josefprusa/Prusa3/box_frame/doc/framestep1.png

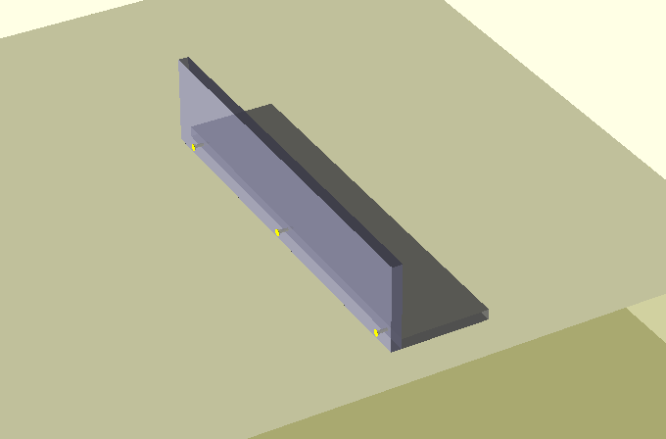
box_frame/doc/framestep1.png
