josefprusa/Prusa3/box_frame/doc/framestep2.png

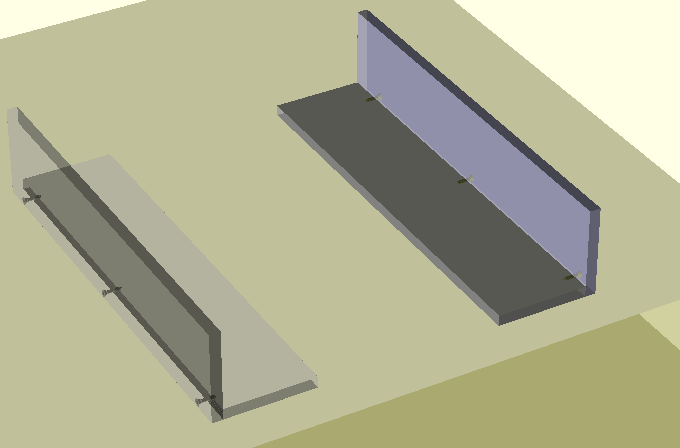
box_frame/doc/framestep2.png
