josefprusa/Prusa3/box_frame/doc/framestep4.png

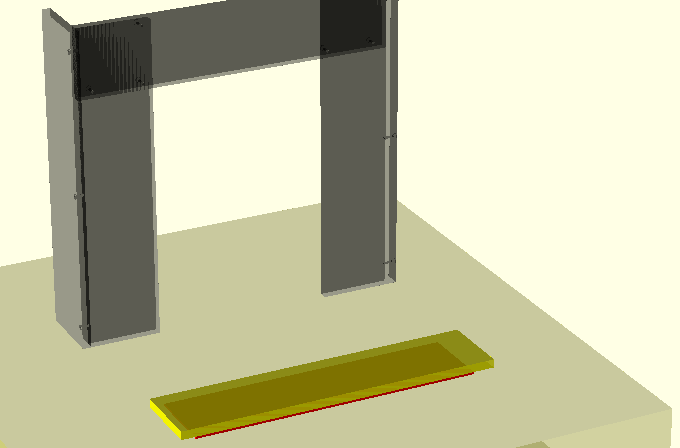
box_frame/doc/framestep4.png
