josefprusa/Prusa3/box_frame/doc/framestep5.png

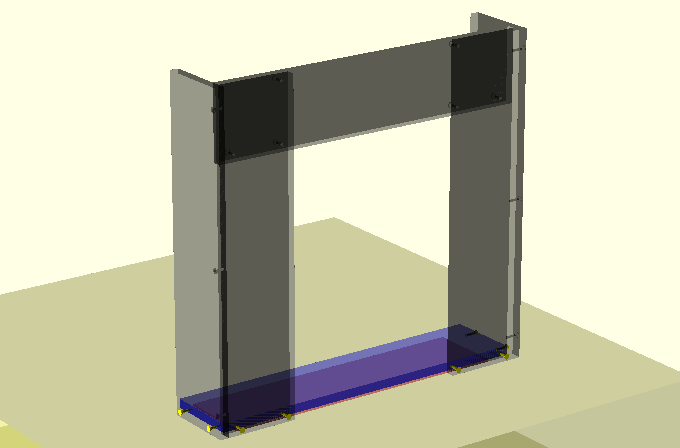
box_frame/doc/framestep5.png
