josefprusa/Prusa3/box_frame/doc/ystep2.png

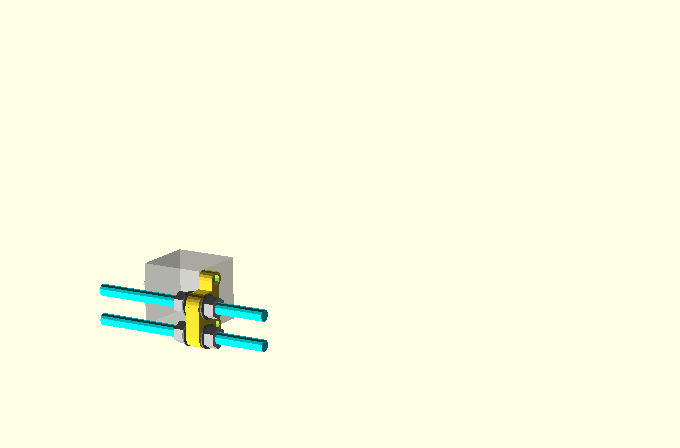
box_frame/doc/ystep2.png
