josefprusa/Prusa3/box_frame/doc/ystep4.png

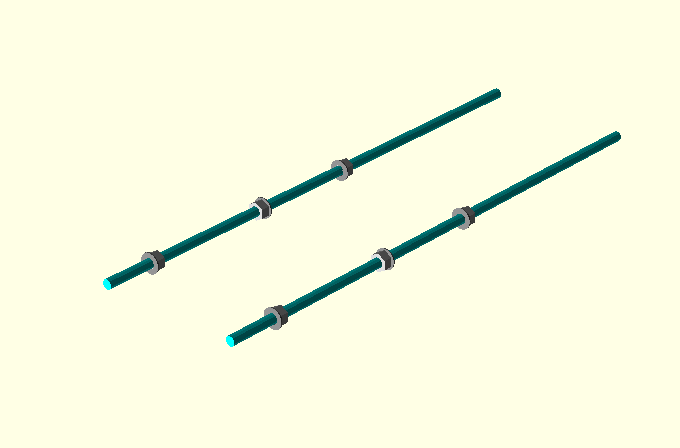
box_frame/doc/ystep4.png
