josefprusa/Prusa3/box_frame/doc/ystep6.png

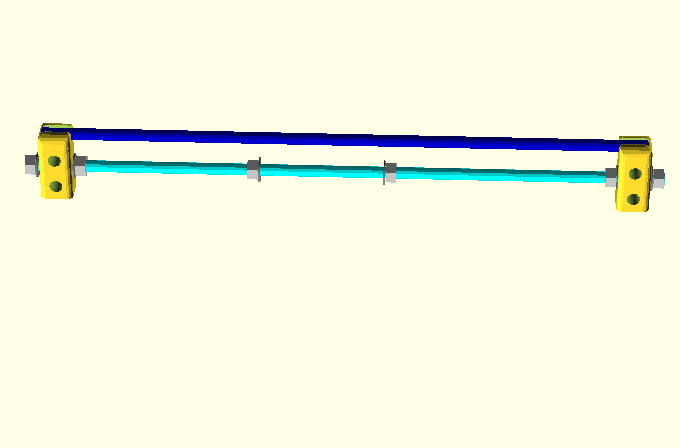
box_frame/doc/ystep6.png
