josefprusa/Prusa3/box_frame/doc/ystep8.png

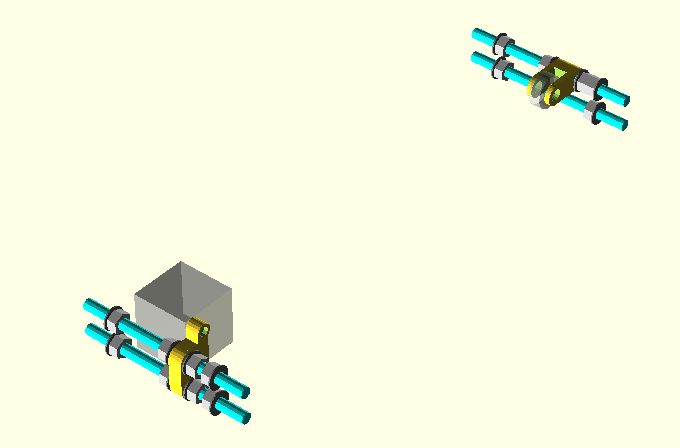
box_frame/doc/ystep8.png
