josefprusa/Prusa3/box_frame/doc/ystep9.png

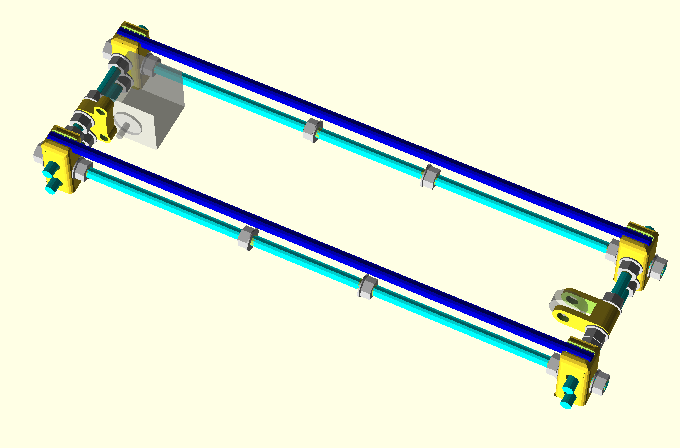
box_frame/doc/ystep9.png
