josefprusa/Prusa3/box_frame/doc/ystep10.png

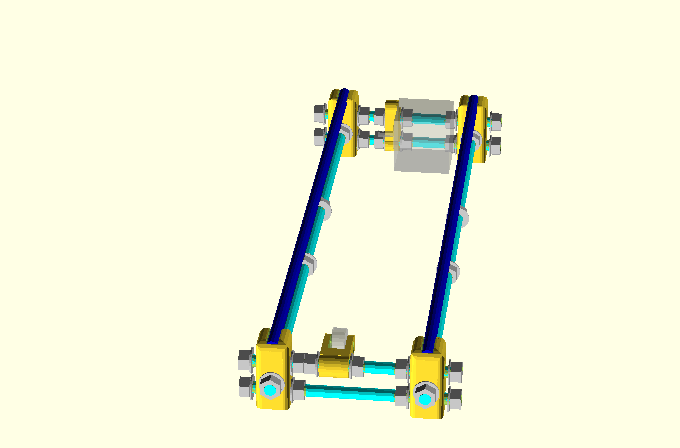
box_frame/doc/ystep10.png
