josefprusa/Prusa3/box_frame/doc/ystep11.png

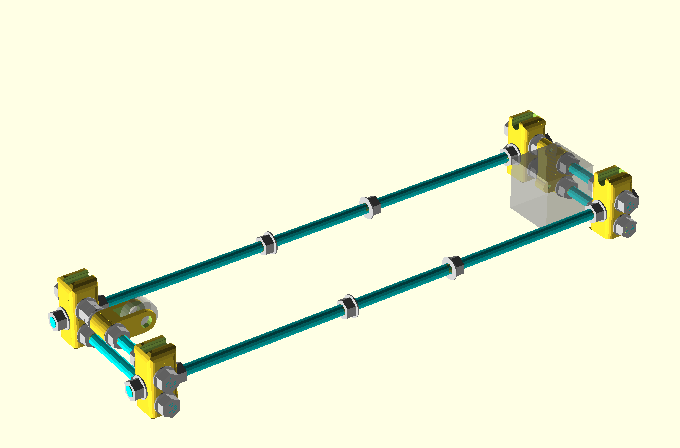
box_frame/doc/ystep11.png
