josefprusa/Prusa3/box_frame/sample_stls/big_htd3_lm12luu/y-drivetrain.stl

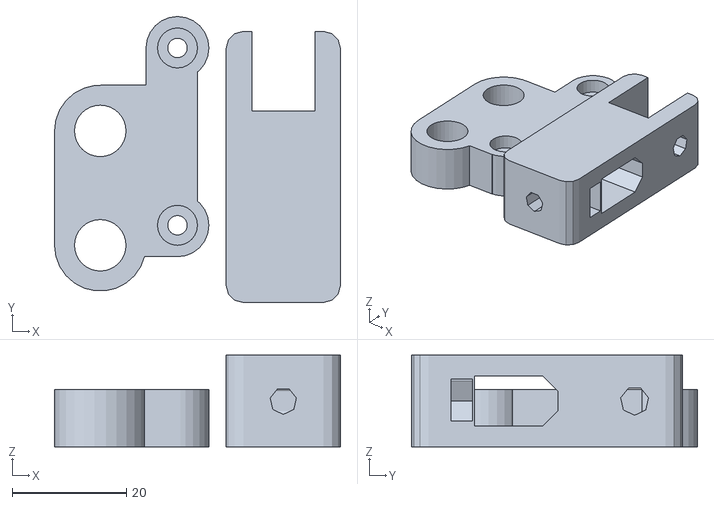
[picture p31: CAD file, 2013-10-11]
box_frame/sample_stls/big_htd3_lm12luu/y-drivetrain.stl
50.0 x 50.0 x 16.0
