josefprusa/Prusa3/box_frame/sample_stls/default_box_gt2_lm10uu/bushing.stl

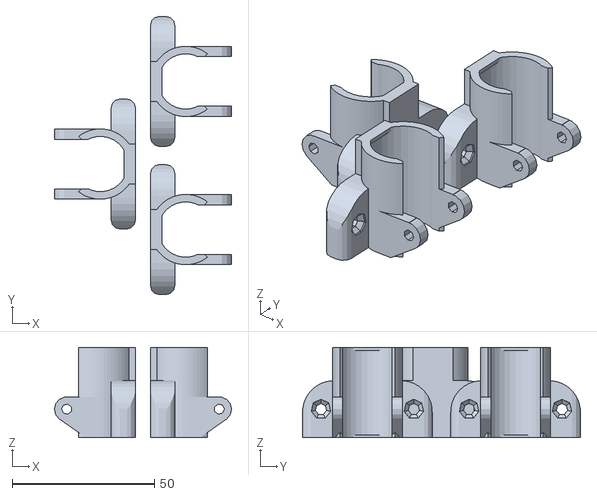
[picture p32: CAD file, 2013-12-24]
box_frame/sample_stls/default_box_gt2_lm10uu/bushing.stl
62.2 x 97.6 x 31.7
