josefprusa/Prusa3/box_frame/sample_stls/default_box_gt2_lm10uu/extras/tube_clamp.stl

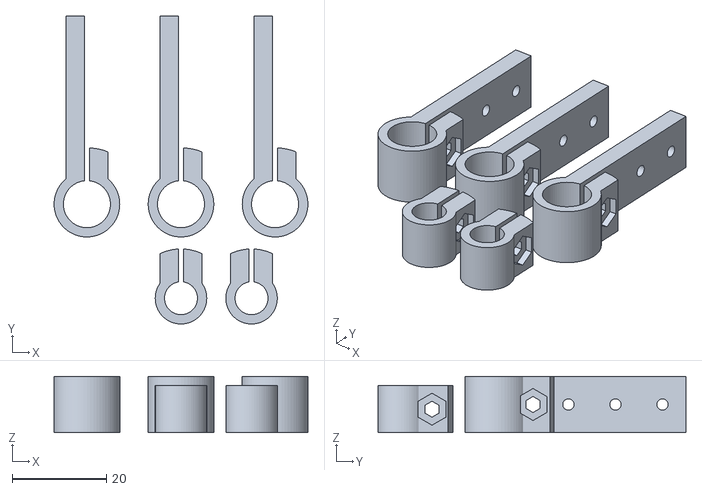
[picture p33: CAD file, 2013-12-24]
box_frame/sample_stls/default_box_gt2_lm10uu/extras/tube_clamp.stl
54.0 x 65.5 x 12.0
