josefprusa/Prusa3/box_frame/sample_stls/single_plate_gt2_lm8uu/y-belt-holder.stl

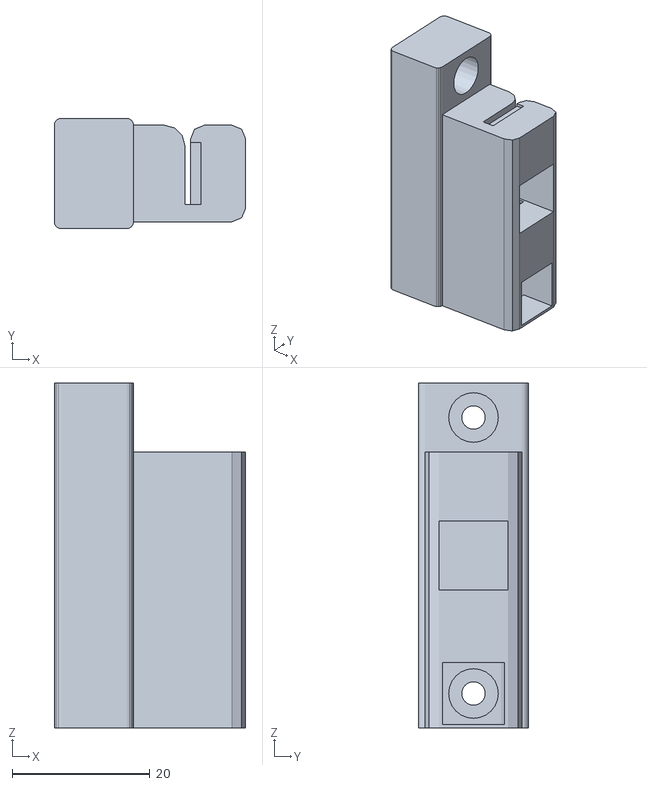
[picture p34: CAD file, 2013-12-24]
box_frame/sample_stls/single_plate_gt2_lm8uu/y-belt-holder.stl
27.8 x 16.0 x 50.0
