josefprusa/Prusa3/mini/extruder/mgs/mgs-idler.stl

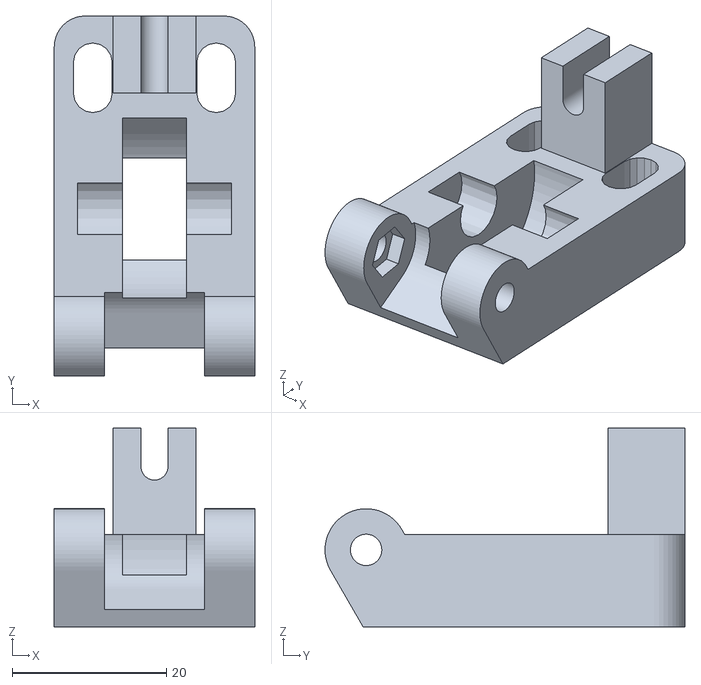
[picture p35: CAD file, 2013-01-09]
mini/extruder/mgs/mgs-idler.stl
26.0 x 46.7 x 25.8
