josefprusa/Prusa3/mini/y-bushing_1x.stl

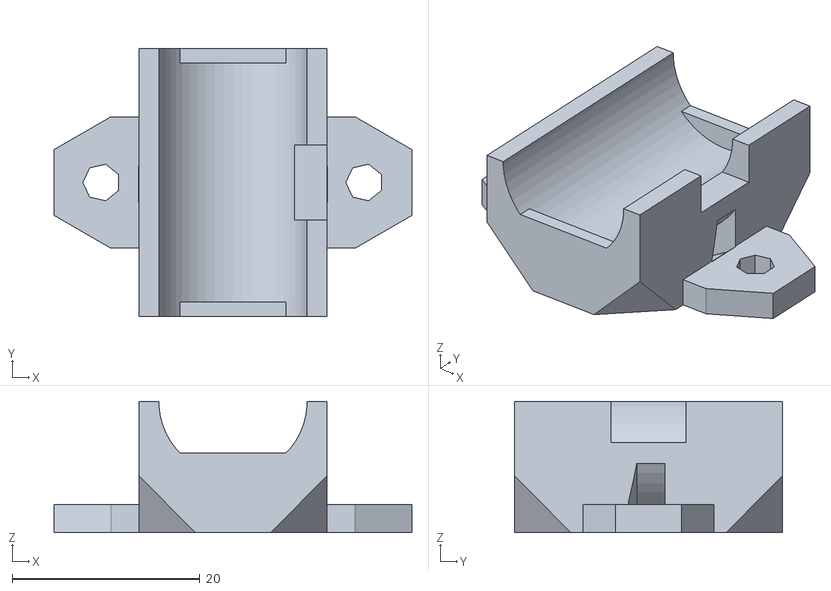
[picture p36: CAD file, 2013-01-09]
mini/y-bushing_1x.stl
38.1 x 28.5 x 14.0
