josefprusa/Prusa3/single_plate/src/frame/6mm/Prusa3ALU-FREZOVANY-v4.dxf

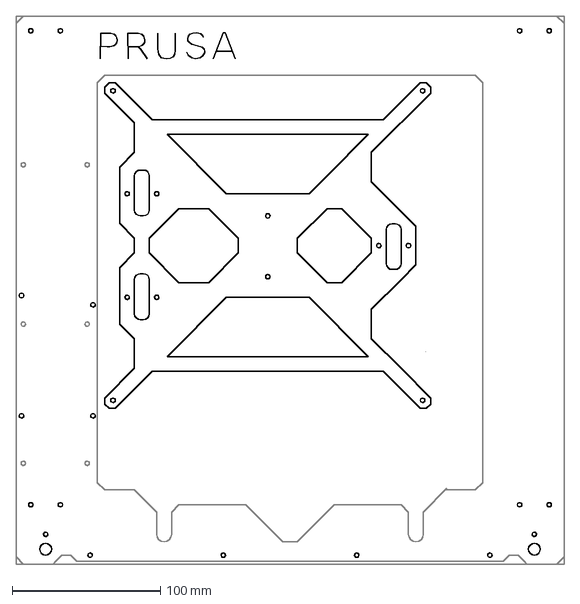
[picture p37: CAD file, 2013-01-09]
single_plate/src/frame/6mm/Prusa3ALU-FREZOVANY-v4.dxf
370.0 x 370.0 mm
