josefprusa/Prusa3/box_frame/sample_stls/big_htd3_lm12luu/z-axis.stl

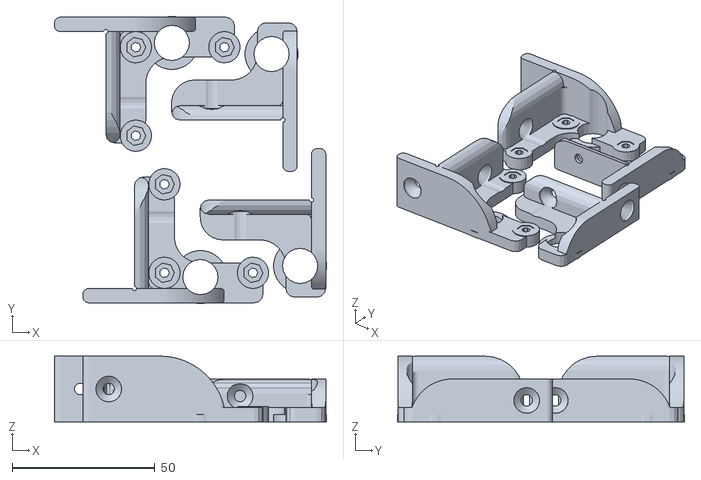
[picture p38: CAD file, 2013-10-11]
box_frame/sample_stls/big_htd3_lm12luu/z-axis.stl
95.2 x 100.5 x 23.0
