josefprusa/Prusa3/box_frame/sample_stls/default_box_gt2_lm10uu/extras/calibrate.stl

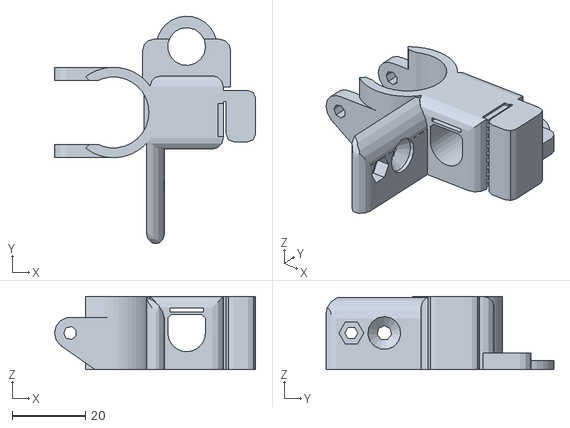
[picture p39: CAD file, 2013-12-24]
box_frame/sample_stls/default_box_gt2_lm10uu/extras/calibrate.stl
54.9 x 62.2 x 20.0
