josefprusa/Prusa3/box_frame/sample_stls/single_plate_gt2_lm8uu/extras/tube_clamp.stl

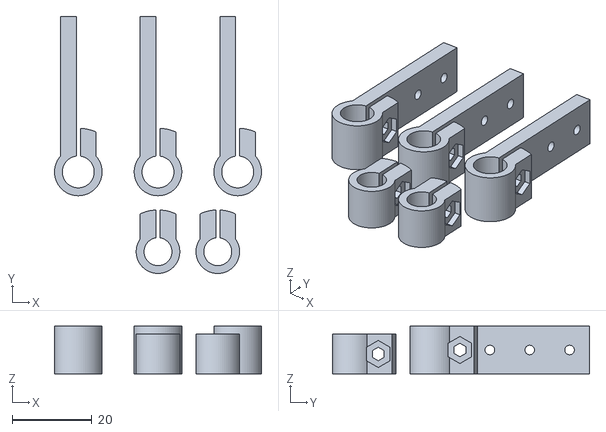
[picture p40: CAD file, 2013-10-11]
box_frame/sample_stls/single_plate_gt2_lm8uu/extras/tube_clamp.stl
52.0 x 64.5 x 12.0
