josefprusa/Prusa3/box_frame/sample_stls/single_plate_gt2_lm8uu/z-axis.stl

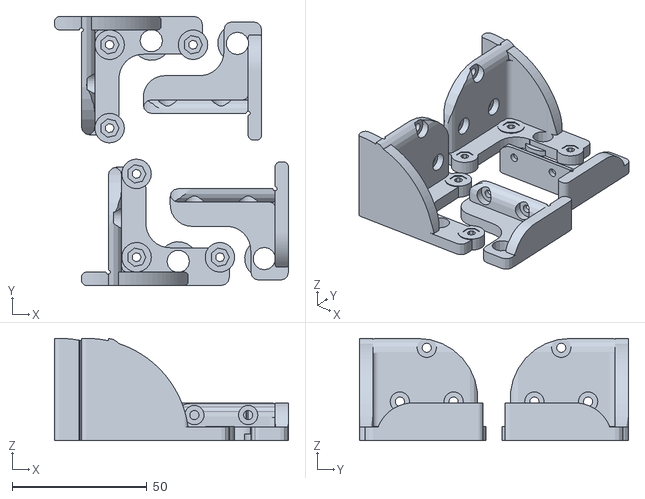
[picture p41: CAD file, 2013-12-24]
box_frame/sample_stls/single_plate_gt2_lm8uu/z-axis.stl
87.0 x 100.0 x 38.0
