josefprusa/Prusa3/mini/extruder/mgs/mgs-groovemount_ABS.stl

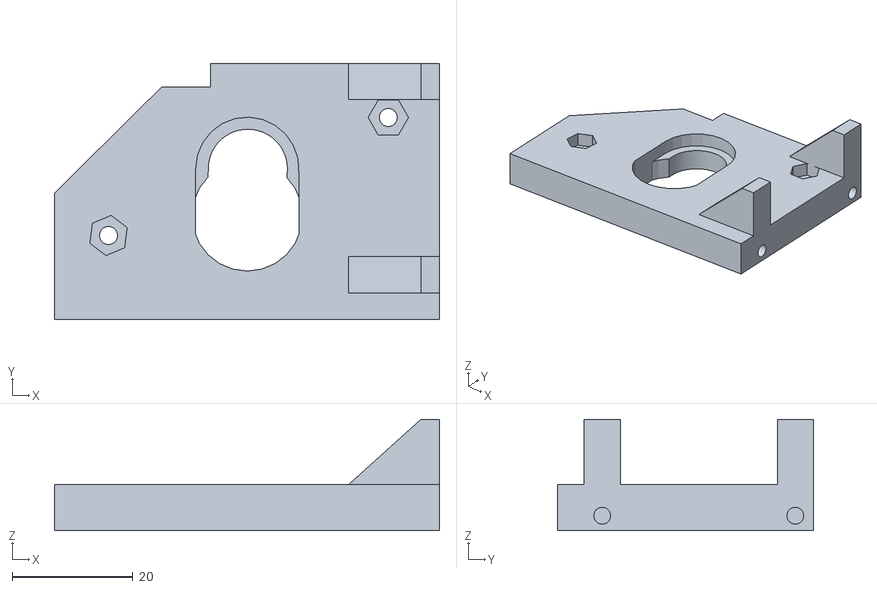
[picture p42: CAD file, 2013-01-09]
mini/extruder/mgs/mgs-groovemount_ABS.stl
63.8 x 42.4 x 18.4
