josefprusa/Prusa3/mini/x-end-motor.stl

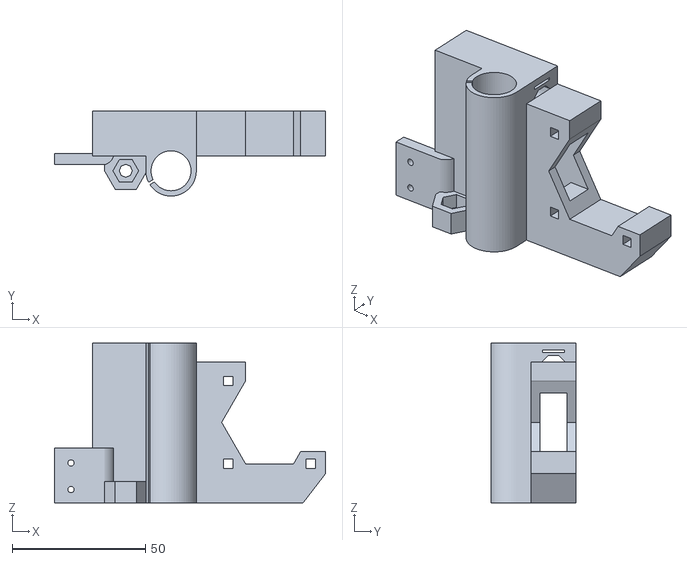
[picture p43: CAD file, 2013-01-09]
mini/x-end-motor.stl
101.8 x 32.0 x 60.0
