josefprusa/Prusa3/single_plate/src/frame/6mm/frame-one-layer.dxf

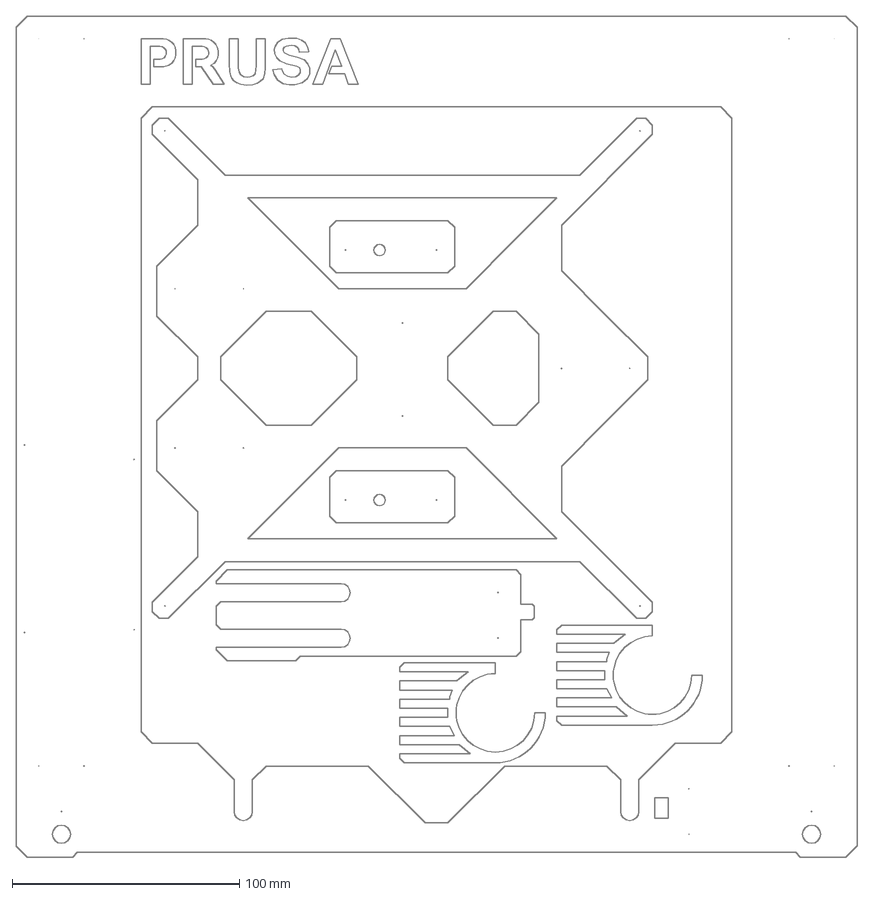
[picture p44: CAD file, 2013-01-09]
single_plate/src/frame/6mm/frame-one-layer.dxf
370.0 x 370.0 mm
