josefprusa/Prusa3/box_frame/sample_stls/big_htd3_lm12luu/y-belt-holder.stl

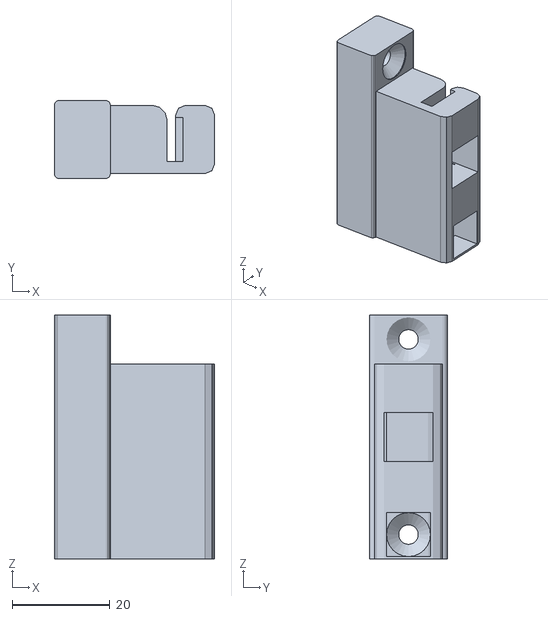
[picture p45: CAD file, 2013-09-17]
box_frame/sample_stls/big_htd3_lm12luu/y-belt-holder.stl
32.9 x 16.0 x 50.0
