josefprusa/Prusa3/box_frame/sample_stls/single_plate_gt2_lm8uu/extras/bearing-holder-single-plate-y.stl

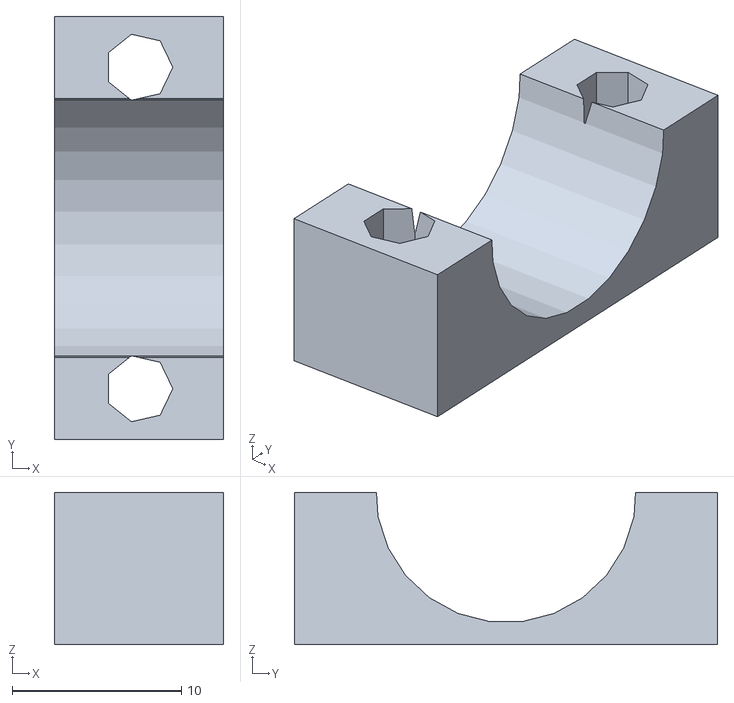
[picture p46: CAD file, 2013-04-29]
box_frame/sample_stls/single_plate_gt2_lm8uu/extras/bearing-holder-single-plate-y.stl
10.0 x 25.0 x 9.00
