josefprusa/Prusa3/box_frame/sample_stls/single_plate_gt2_lm8uu/x-carriage.stl

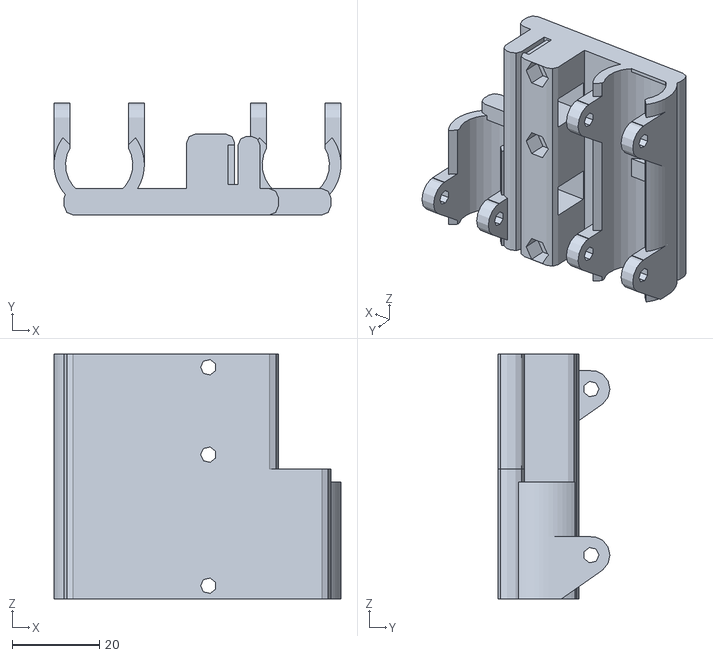
[picture p47: CAD file, 2013-12-24]
box_frame/sample_stls/single_plate_gt2_lm8uu/x-carriage.stl
65.7 x 25.6 x 56.0
