josefprusa/Prusa3/mini/z-bottom-right.stl

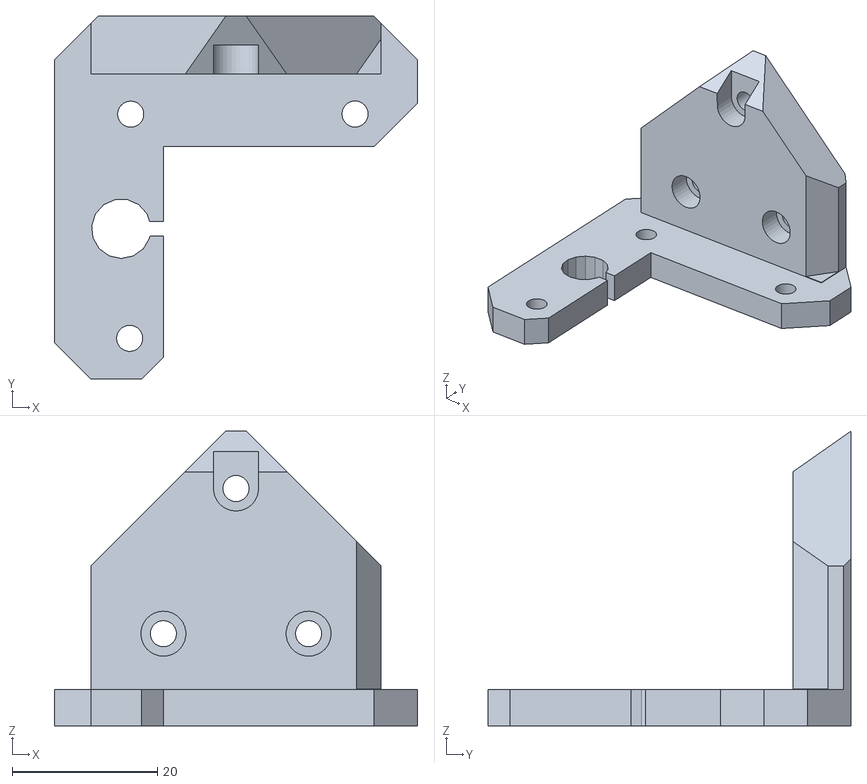
[picture p48: CAD file, 2013-01-09]
mini/z-bottom-right.stl
50.0 x 50.0 x 40.6
