josefprusa/Prusa3/box_frame/sample_stls/big_htd3_lm12luu/x-carriage.stl

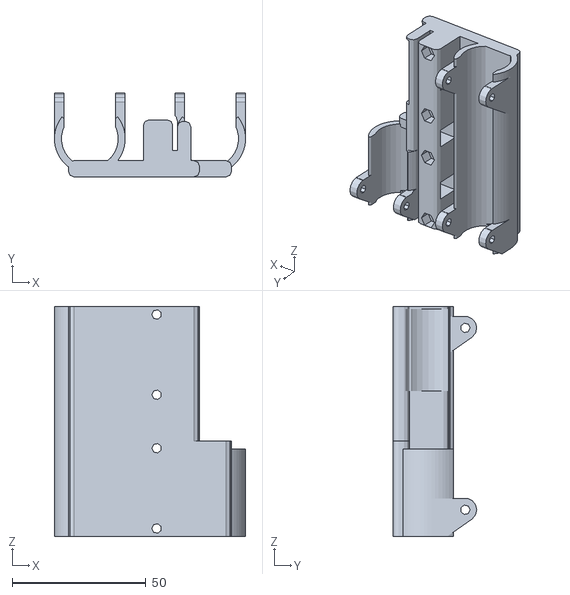
[picture p49: CAD file, 2013-09-17]
box_frame/sample_stls/big_htd3_lm12luu/x-carriage.stl
71.5 x 31.2 x 86.0
