josefprusa/Prusa3/box_frame/sample_stls/default_box_gt2_lm10uu/x-carriage.stl

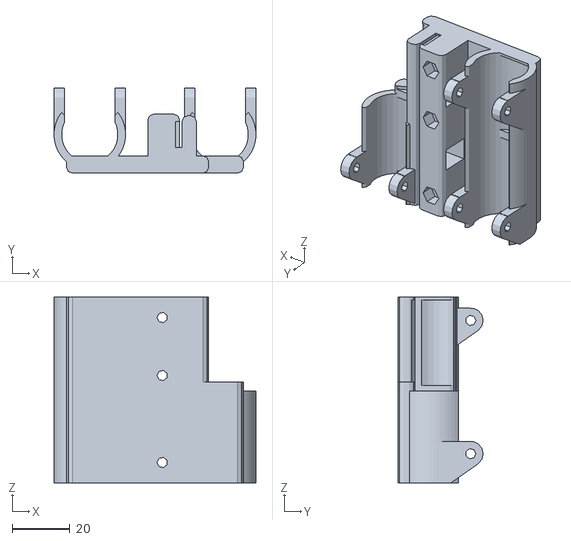
[picture p50: CAD file, 2013-12-24]
box_frame/sample_stls/default_box_gt2_lm10uu/x-carriage.stl
69.7 x 29.4 x 64.0
