josefprusa/Prusa3/box_frame/sample_stls/single_plate_gt2_lm8uu/x-end.stl

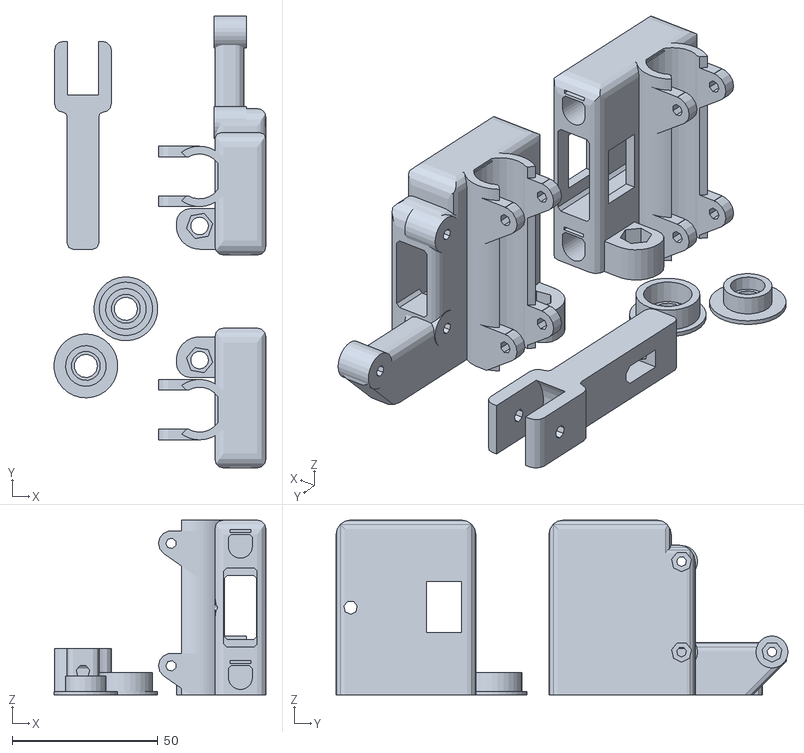
[picture p51: CAD file, 2013-12-24]
box_frame/sample_stls/single_plate_gt2_lm8uu/x-end.stl
72.7 x 155.0 x 60.0
