josefprusa/Prusa3/mini/y-motor.stl

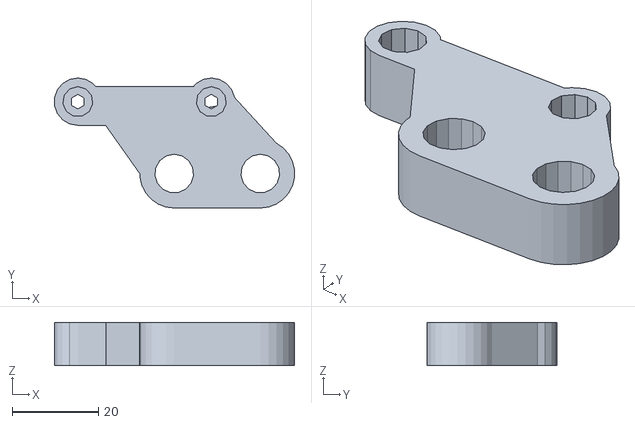
[picture p52: CAD file, 2013-01-09]
mini/y-motor.stl
55.7 x 30.2 x 10.0
