josefprusa/Prusa3/box_frame/sample_stls/default_box_gt2_lm10uu/y-belt-holder.stl

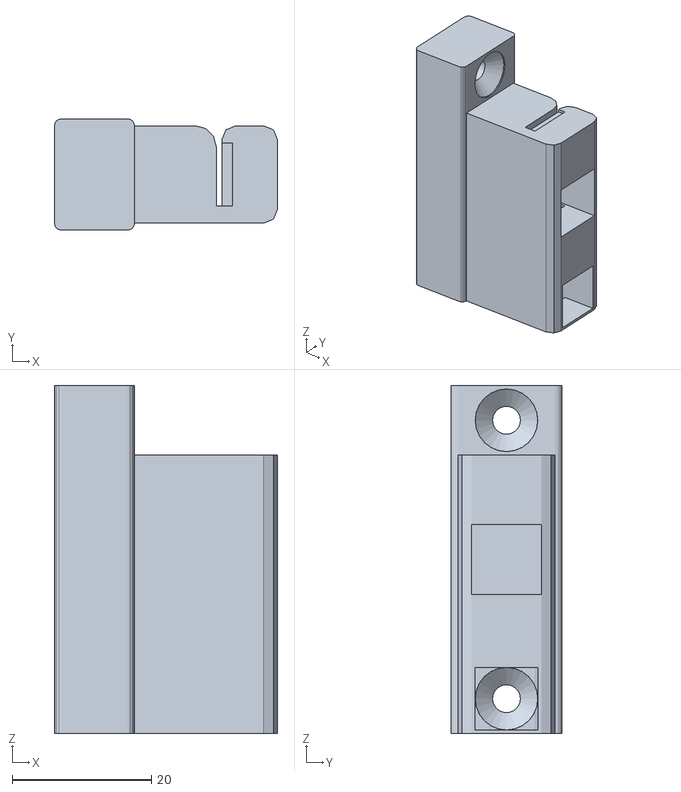
[picture p53: CAD file, 2013-12-24]
box_frame/sample_stls/default_box_gt2_lm10uu/y-belt-holder.stl
32.0 x 16.0 x 50.0
