josefprusa/Prusa3/mini/y-endstop-holder.stl

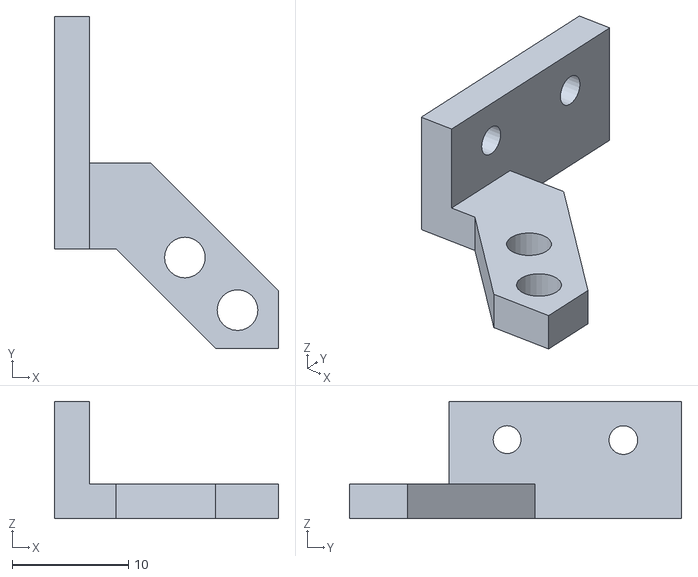
[picture p54: CAD file, 2013-01-09]
mini/y-endstop-holder.stl
19.3 x 28.6 x 10.1
