josefprusa/Prusa3/box_frame/sample_stls/big_htd3_lm12luu/y-axis-bracket.stl

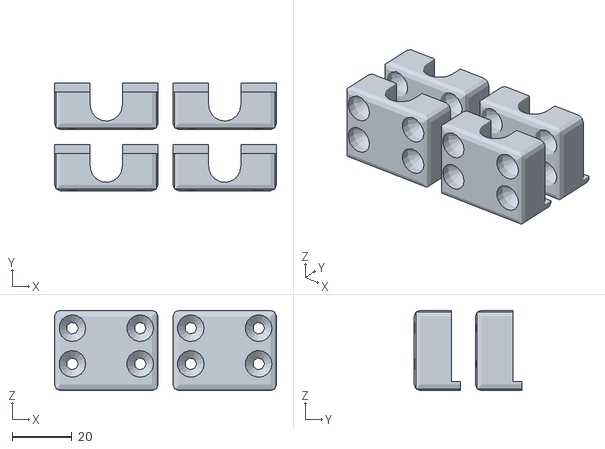
[picture p55: CAD file, 2013-06-04]
box_frame/sample_stls/big_htd3_lm12luu/y-axis-bracket.stl
74.6 x 36.2 x 27.0
