josefprusa/Prusa3/mini/frame-mount.stl

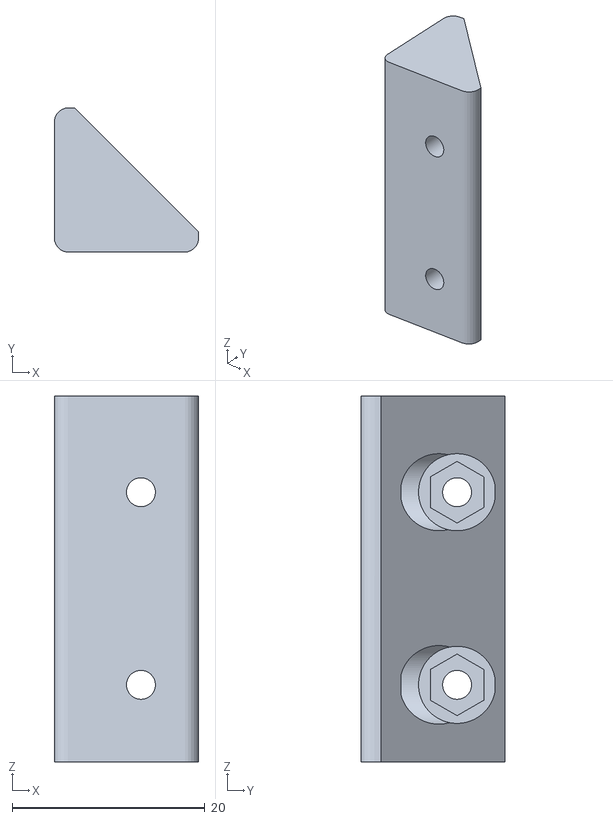
[picture p56: CAD file, 2013-01-09]
mini/frame-mount.stl
15.0 x 15.0 x 38.0
