josefprusa/Prusa3/mini/y-corners_4x.stl

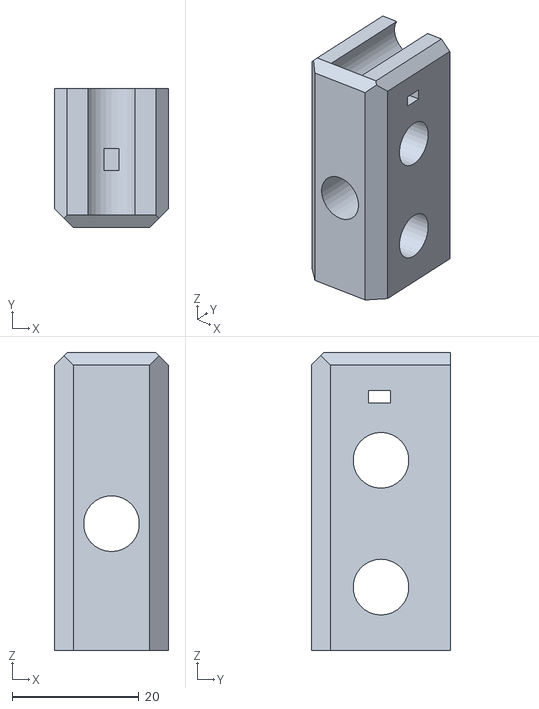
[picture p57: CAD file, 2013-01-09]
mini/y-corners_4x.stl
18.0 x 22.0 x 47.0
