josefprusa/Prusa3/mini/y-belt-holder.stl

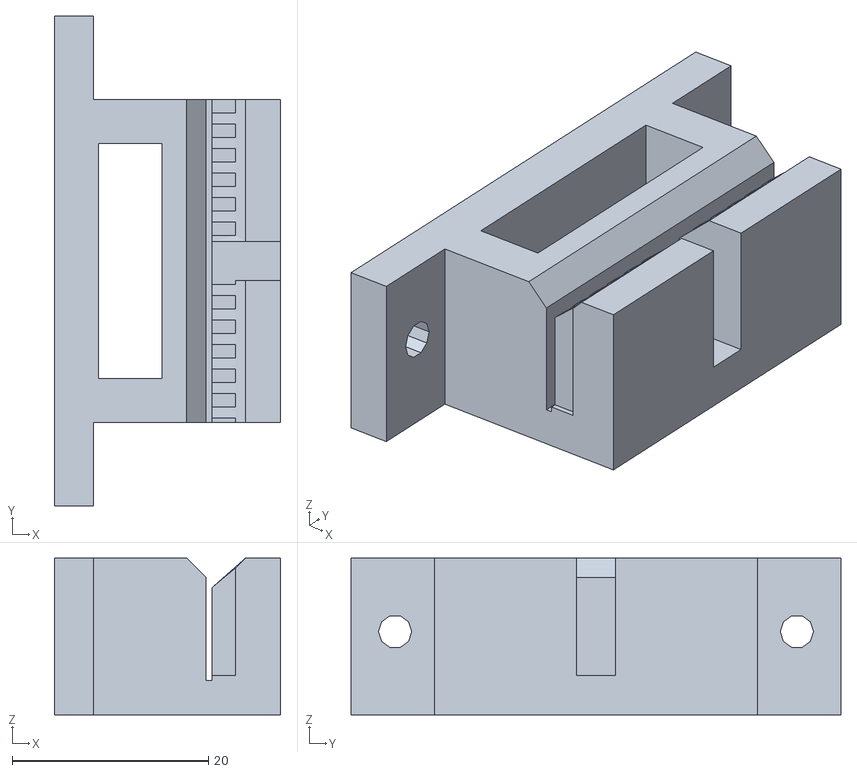
[picture p58: CAD file, 2013-01-09]
mini/y-belt-holder.stl
23.1 x 50.0 x 16.0
