josefprusa/Prusa3/mini/z-top-right.stl

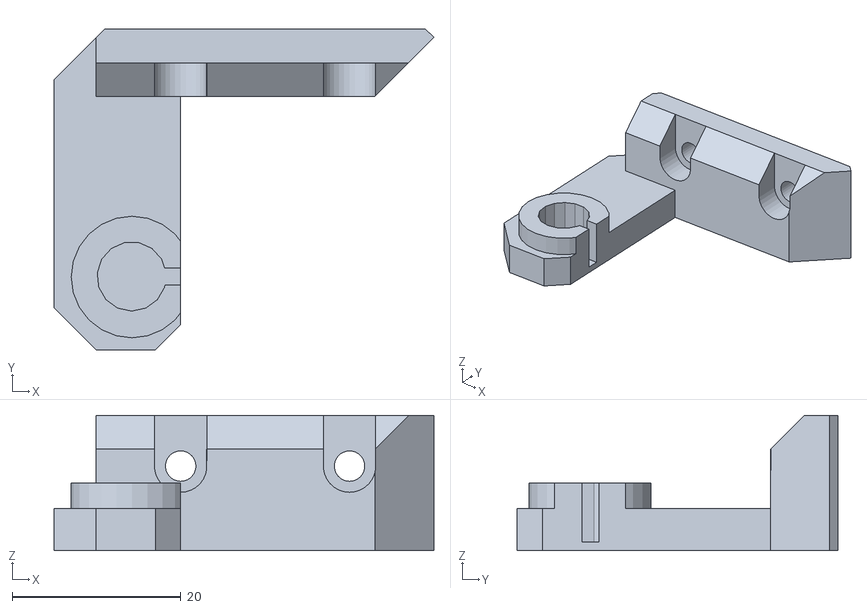
[picture p59: CAD file, 2013-01-09]
mini/z-top-right.stl
45.0 x 38.0 x 16.0
