josefprusa/Prusa3/mini/x-carriage.stl

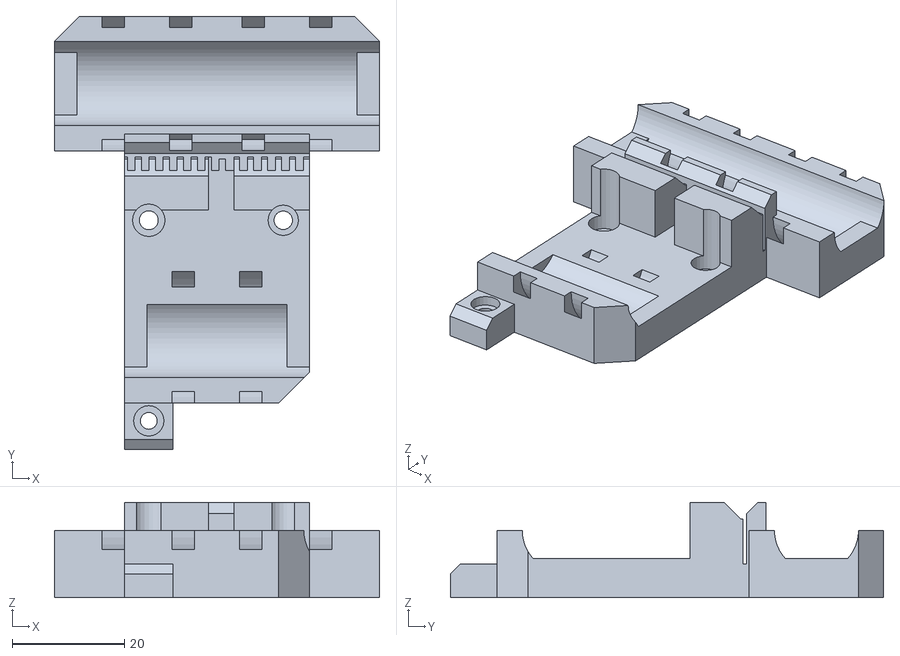
[picture p60: CAD file, 2013-01-09]
mini/x-carriage.stl
58.0 x 77.4 x 17.0
