josefprusa/Prusa3/mini/x-end-idler.stl

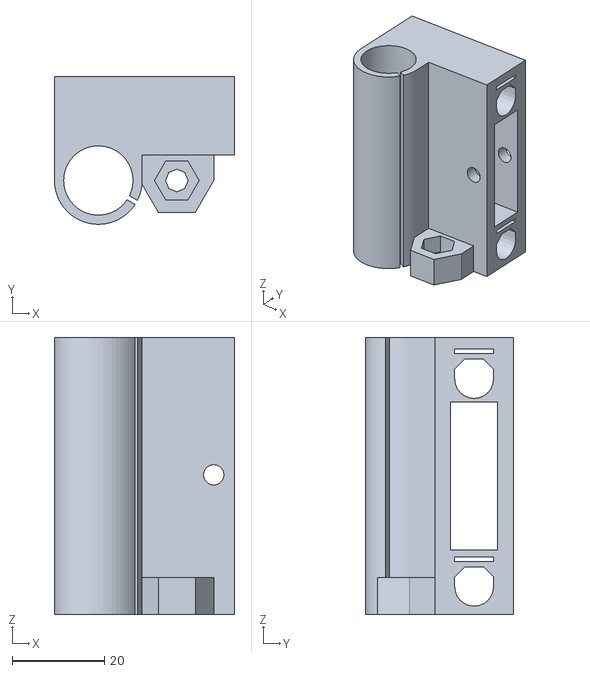
[picture p61: CAD file, 2013-01-09]
mini/x-end-idler.stl
39.0 x 32.0 x 60.0
