josefprusa/Prusa3/mini/z-endstop-holder.stl

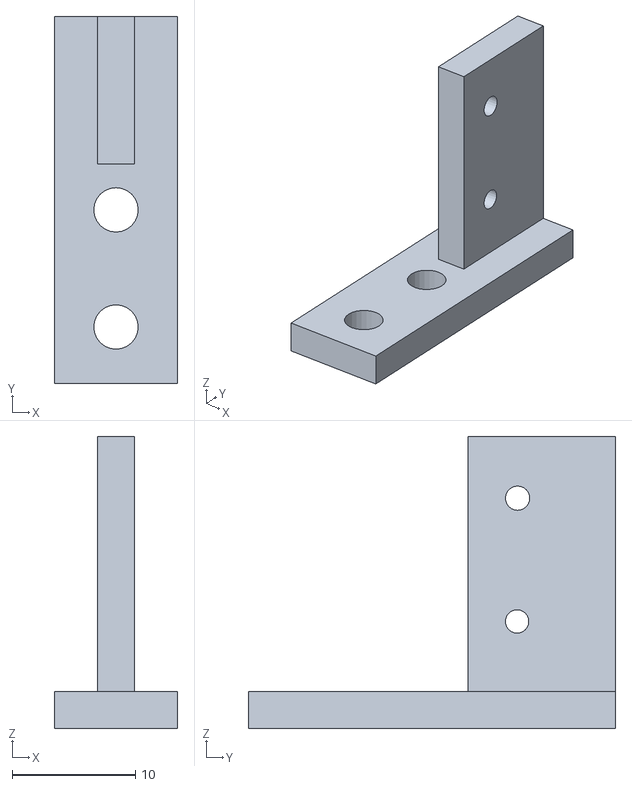
[picture p62: CAD file, 2013-01-09]
mini/z-endstop-holder.stl
10.0 x 29.8 x 23.7
