josefprusa/Prusa3/box_frame/bushing.scad

// PRUSA iteration3
// Bushing/bearing housings
// GNU GPL v3
// Josef Průša <josefprusa@me.com>
// Václav 'ax' Hůla <axtheb@gmail.com>
// http://www.reprap.org/wiki/Prusa_Mendel
// http://github.com/josefprusa/Prusa3

// ThingDoc entry
/**
 * @id yBearingHolder
 * @name Y Axis Bearing Holder
 * @category Printed
 */
 
include <configuration.scad>

// ensure that the part length is at least the length of bushing barrel plus add
function adjust_bushing_len(conf_b, h, add=layer_height*2) = ((conf_b[2]+add) > h) ? conf_b[2]+add : h;

//distance from the flat side of bushing holder to rod center
function bushing_foot_len(conf_b, h=10.5, add=4*single_wall_width) = ((conf_b[1]+add) > h) ? conf_b[1]+add : h;

function bushing_outer_radius(conf_b) = conf_b[1] + 4*single_wall_width;

// basic building blocks, housings for 1 bushing/bearing
// at [0,0] there is center of the smooth rod, pointing in Z

module linear_bushing_negative_single(conf_b=bushing_xy, h=0){
    // barrel with the dimensions of a bushing/bearing
    // to be substracted as needed
    translate([0, 0, -0.01])  cylinder(r = conf_b[1], h = adjust_bushing_len(conf_b, h) + 0.02);
}

module linear_bearing_negative_single(conf_b=bushing_xy, h=0, shadow=false){
    // barrel with the dimensions of the bearing
    translate([0, 0, -0.01 + 3 * layer_height])  cylinder(r = conf_b[1], h = adjust_bushing_len(conf_b, h) + 0.02);
    if (shadow == false) {
        translate([0, -conf_b[1]+1, -0.01 + 3 * layer_height]) cube([30, 2 * conf_b[1] - 2, adjust_bushing_len(conf_b, h) + 0.02]);
    }
}

module linear_bushing_single(conf_b=bushing_xy, h=0) {
    // This is the printed barrel around bushing
    // with foot pointing to -x
    translate([-bushing_foot_len(conf_b), -7, 0]) cube([bushing_foot_len(conf_b), 14, adjust_bushing_len(conf_b, h)]);
    cylinder(r=bushing_outer_radius(conf_b), h=adjust_bushing_len(conf_b, h));
}

module linear_bushing_negative(conf_b=bushing_xy, h=0){
    // return simple negative stretched all along and a smooth rod
    translate([0,0,-0.1]) cylinder(r = conf_b[0] + single_wall_width, h=adjust_bushing_len(conf_b, h)+0.2);
    linear_bushing_negative_single(conf_b, h=adjust_bushing_len(conf_b, h));
}

module linear_bearing_negative(conf_b = bushing_xy, h = 0, shadow=false){
    //same as linear_bushing_negative, but with z direction constrained parts
    translate([0,0,-0.1]) cylinder(r = conf_b[0] + single_wall_width, h=adjust_bushing_len(conf_b, h, 8*layer_height)+0.2);
    //lower bearing
    linear_bearing_negative_single(conf_b, 0, shadow);
    if (h > 2*conf_b[2] + 9*layer_height){
        translate([0,0,h]) mirror([0,0,1]) linear_bearing_negative_single(conf_b, 0, shadow);
    }
}

module linear_negative_preclean(conf_b = bushing_xy) {
    // makes sure there is nothing interfering
    // to be substracted before linear()
    cylinder(r = conf_b[1] + single_wall_width, h=300, center=true);
}

module linear_bushing_sloped(conf_b=bushing_xy, h= 100){
    // cut the bushing at angle, so it can be printed upside down
    intersection(){
        linear_bushing_single(conf_b, h = h);
        // hardcoded, may need fixing for different barelled bushings
        // atm there is only one and I am too lazy
        translate([0, 0, -2]) rotate([0,-50,0]) cube([30, 40, 80], center=true);
    }
}

module linear_bushing(conf_b=bushing_xy, h=0){
    // this is the function to be used for type 1 linears (barrel holder)
    // It has bushing on bottom and for parts longer than 3x the barel length on top too
    difference() {
        union() {
            translate([-bushing_foot_len(conf_b), -7, 0]) cube([2, 14, adjust_bushing_len(conf_b, h)]);
            linear_bushing_single(conf_b);
            if (h>3*conf_b[2]) {
                translate([0,0,h]) mirror([0,0,1]) linear_bushing_sloped(conf_b);
            }
        }
        linear_bushing_negative(conf_b, h);
    }
}

module linear_bearing(conf_b=bushing_xy, h=0){
    difference() {
        union() {
            difference(){
                union(){
                    //main block
                    //translate([-bushing_foot_len(conf_b), -7, 0]) cube([4, 14, adjust_bushing_len(conf_b, h, 9*layer_height)]);   <- removed for duplicity:)
                    translate([0,0,0]) cylinder(h = adjust_bushing_len(conf_b, h, 9*layer_height), r=bushing_outer_radius(conf_b), $fn=60);
                }
                //smooth entry cut
                translate([12,0,-1]) rotate([0,0,45]) cube([20, 20, 200], center=true);
            }
            intersection(){
                translate([0, -(bushing_outer_radius(conf_b)), 0]) cube([30, 2*bushing_outer_radius(conf_b) , max(h, conf_b[2] + 9 * layer_height)]);
                union() {
                    // upper clamp for long holders
                    if (h > 2*conf_b[2] + 9*layer_height || conf_b[2] > 45){
                        translate ([0,0, max(h, conf_b[2]) - 8 ]) bearing_clamp(conf_b, 2*(bushing_outer_radius(conf_b)));
                    }
                    //lower clamp
                    translate ([0, 0, 10]) bearing_clamp(conf_b, 2*(bushing_outer_radius(conf_b)));
                }
            }
        }
        //main axis
        translate([0,0,-2]) cylinder(h = adjust_bushing_len(conf_b, h)+10, r=conf_b[1]);
        //main cut
        translate([0, -conf_b[1]+1, -1]) cube([30, 2*conf_b[1]-2, 200]);
    }
    difference() {
        translate([-bushing_foot_len(conf_b), -7, 0]) cube([4, 14, adjust_bushing_len(conf_b, h, 9*layer_height)]);
        linear_negative(conf_b, h);
    }
}

// this should be more parametric
module firm_foot(conf_b = conf_b_lm8uu){
    difference(){
        union() {
            translate([8.5/2,0,0]) cube_fillet([8.5, 42 + xy_delta * 2, 20], top=[11, 0, 11, 0], center=true);
        }
        translate([9, 14.5 + xy_delta, 0]) rotate([0, -90, 0]) screw(head_drop=1, $fn=small_hole_segments);
        translate([9,-14.5 - xy_delta, 0]) rotate([0,-90,0]) screw(head_drop=1,$fn=small_hole_segments);
    }
}

module y_bearing(conf_b=bushing_xy){

    difference() {
        union() {
            difference() {
                union() {
                    translate([-bushing_foot_len(conf_b), 0, 10]) firm_foot();
                    if (bushing_xy[2] > 45) {
                        translate([-bushing_foot_len(conf_b), 0, adjust_bushing_len(bushing_xy, 45) - 8]) mirror([0, 0, 1]) firm_foot();
                    }
                }
                linear_negative_preclean();
            }
            linear();
        }
        //linear_negative(bushing_xy, 20);
    }
}

module bearing_clamp_brick(conf_b, h){
    translate([-(m4_nut_diameter/2+conf_b[1]), 0, 0])
        cube([m4_nut_diameter + 2 * conf_b[1], m4_nut_diameter + 1, h], center = true);
}

module bearing_clamp(conf_b=bushing_xy, h=0){
    // inspired by John Ridley and Jonas Kühling
    rotate([90, 0, 0]) {
        difference(){
            union(){
                translate([m3_diameter / 2 + conf_b[1] + 0.3, 0, 0])
                    cylinder(h=h, r = m4_nut_diameter / 2 + 0.5, center = true);
                translate([m3_diameter / 2 + conf_b[1] + 0.3, 0, 0]) {
                    bearing_clamp_brick(conf_b, h);
                    rotate([0,0,35])
                        bearing_clamp_brick(conf_b, h);
                }
            }
            translate([m3_diameter / 2 + conf_b[1] + 0.3, 0, 0]) {
                cylinder(r=m3_diameter / 2, h=h+2, center=true,$fn=small_hole_segments);
                %cylinder(r=m3_diameter / 2, h=h+2, center=true,$fn=small_hole_segments);
            }
        }
    }
}


module linear_negative(conf_b = bushing_xy, h = 0, shadow=false){
    //selects right negative based on type
    if (conf_b[3] == 0) {
        linear_bearing_negative(conf_b, h, shadow);
    } else {
        linear_bushing_negative(conf_b, h, shadow);
    }
}

module linear(conf_b = bushing_xy, h = 0){
    //selects right model based on type
    if (conf_b[3] == 0) {
        linear_bearing(conf_b, h);
    } else {
        linear_bushing(conf_b, h);
    }
    %linear_negative(conf_b, h, true);
}

if (i_am_box == 1) {
    %cylinder(r=bushing_xy[0], h=90);

    y_bearing();
    translate([0,52,0]) y_bearing();

    if (bushing_xy[2] < 45) {
        translate ([-30,23,0]) mirror([1,0,0]) y_bearing();
    }
} else {
    cube([0.1, 0.1, 0.1]);
}
